connorwk/Bendix_G-15_Boards/G15_Gold_FF/G15_Gold_FF_Back.png

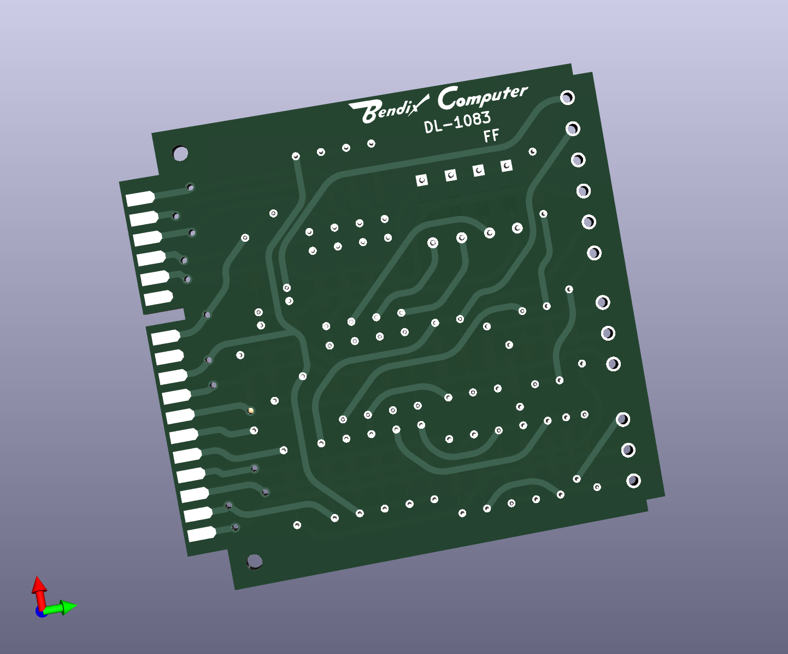
G15_Gold_FF/G15_Gold_FF_Back.png
